DimAnge/mimic/docs/assets/photos/desk.jpg

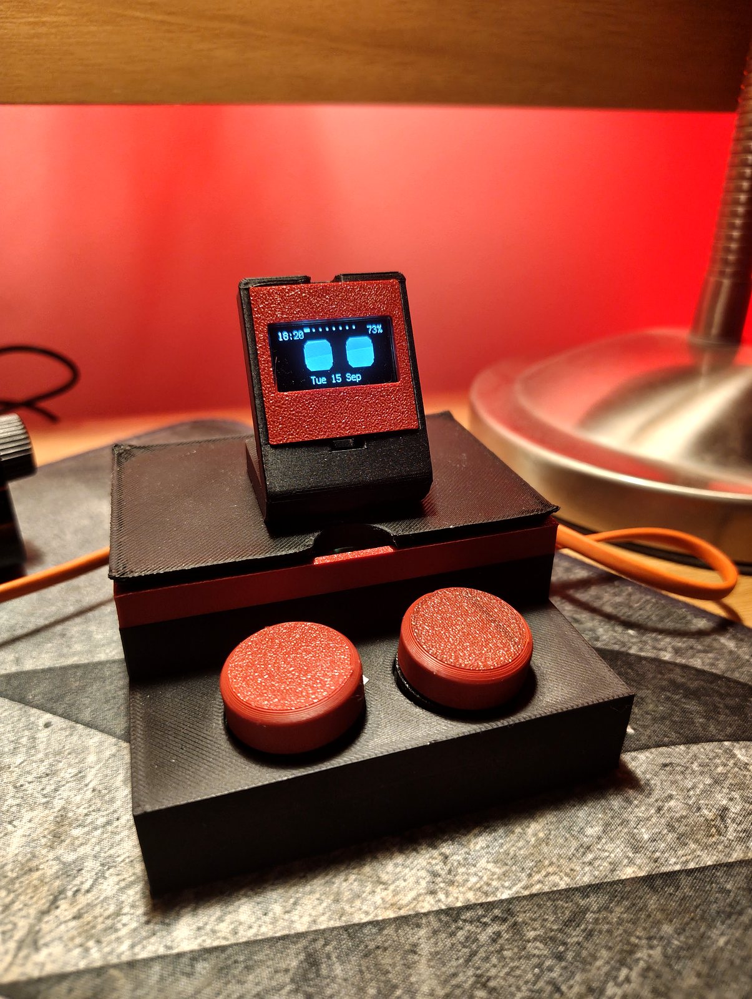
docs/assets/photos/desk.jpg
