DimAnge/mimic/docs/assets/photos/games.jpg

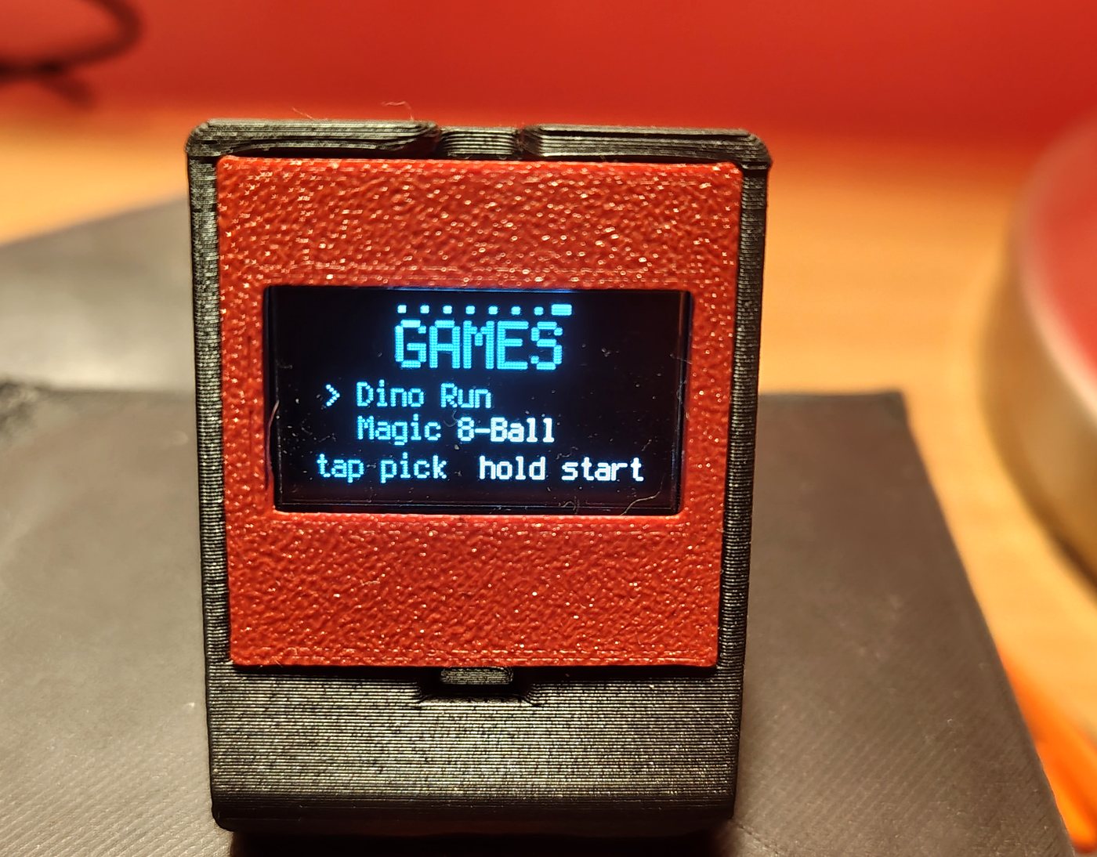
docs/assets/photos/games.jpg
