DimAnge/mimic/docs/assets/shots/calendar.png

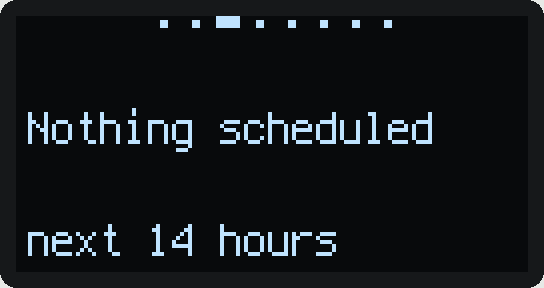
docs/assets/shots/calendar.png
