DimAnge/mimic/docs/assets/shots/eightball.png

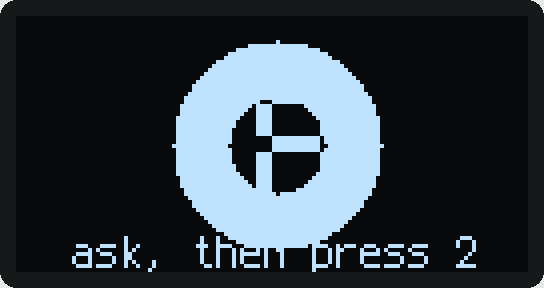
docs/assets/shots/eightball.png
