DimAnge/mimic/docs/assets/shots/face.png

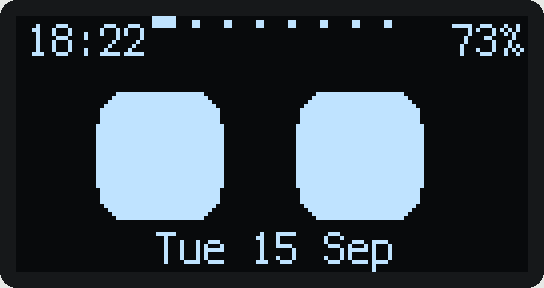
docs/assets/shots/face.png
