DimAnge/mimic/docs/assets/shots/games.png

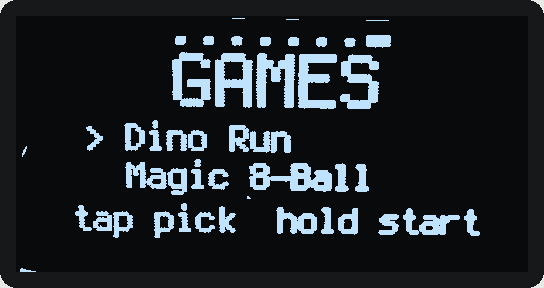
docs/assets/shots/games.png
