DimAnge/mimic/docs/assets/shots/spotify.png

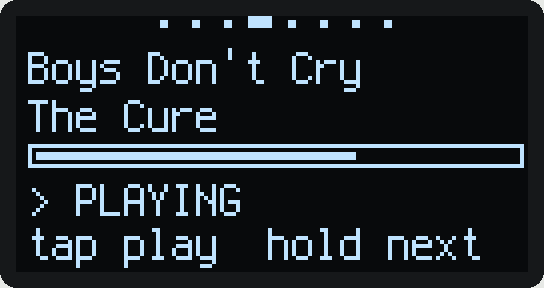
docs/assets/shots/spotify.png
