DimAnge/mimic/docs/assets/social-preview.png

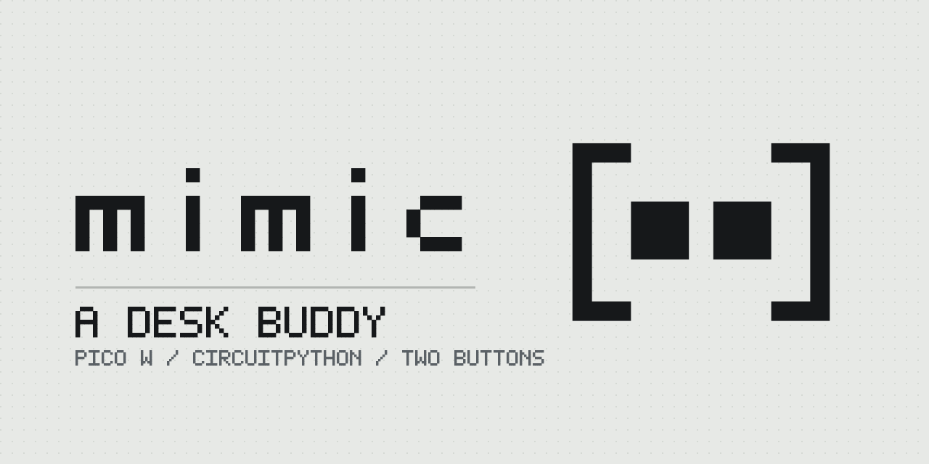
docs/assets/social-preview.png
