DimAnge/mimic/docs/assets/photos/usage.jpg

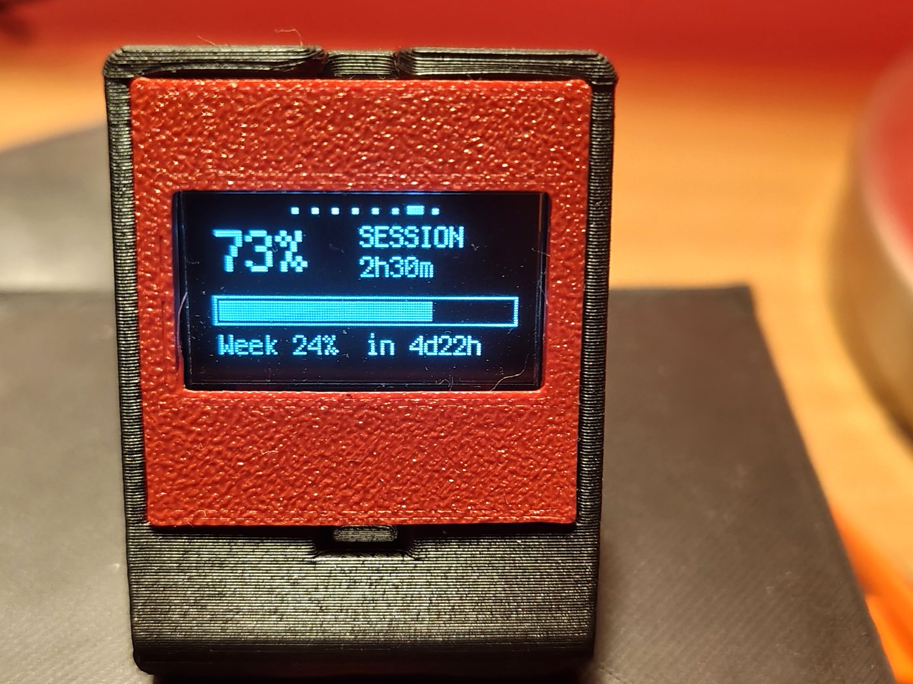
docs/assets/photos/usage.jpg
