DimAnge/mimic/docs/assets/shots/usage.png

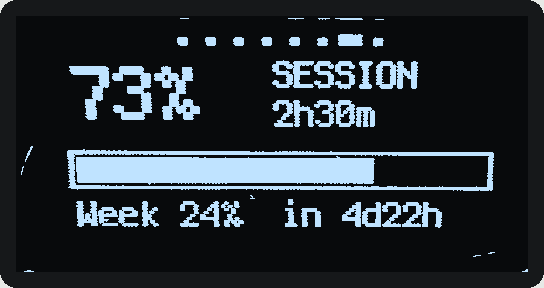
docs/assets/shots/usage.png
