DimAnge/mimic/docs/assets/wiring.png

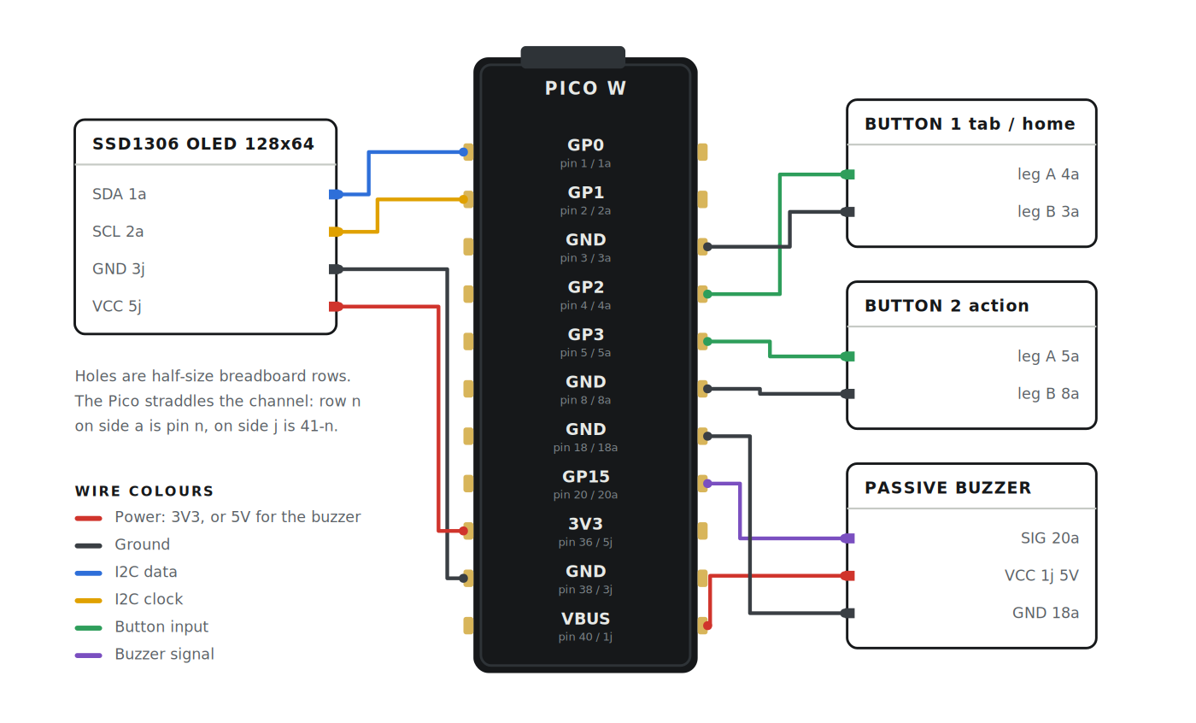
docs/assets/wiring.png
